MuriloLD/Projeto-AT-SP/Peças 3D/chave_On_Off/Bot/vistas_chaveOnOff_bot.PDF

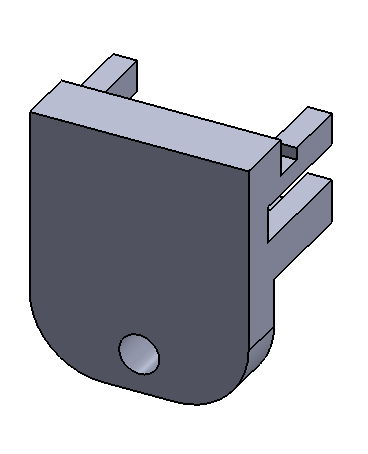
[picture p1: figure]
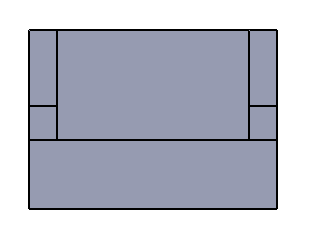
[picture p2: figure]
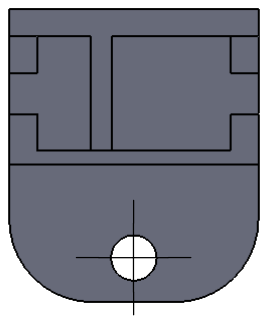
[picture p3: figure]
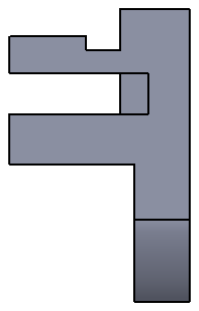
[picture p4: figure]
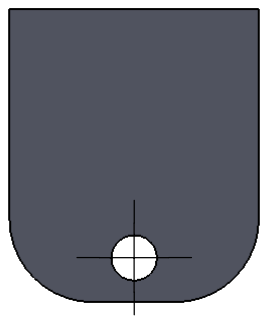
[picture p5: figure]
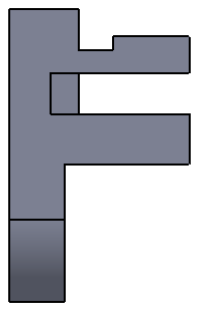
[picture p6: figure]
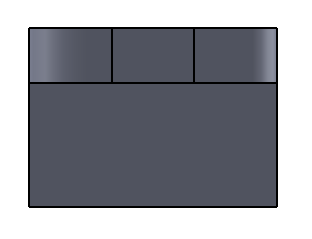
[picture p7: figure]
