MuriloLD/Projeto-AT-SP/Arquivos EAGLE/Shield ESP8266/shieldEsp_pcb.png

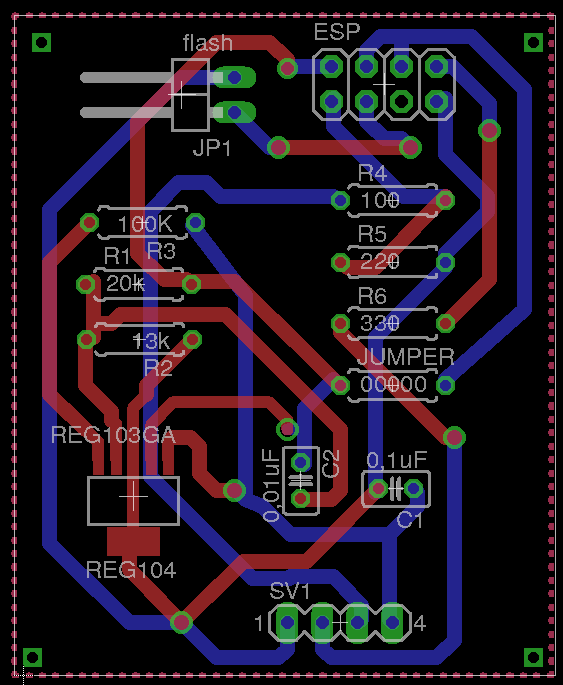
Arquivos EAGLE/Shield ESP8266/shieldEsp_pcb.png
