MuriloLD/Projeto-AT-SP/Peças 3D/case_bateria/Top/cotas.PNG

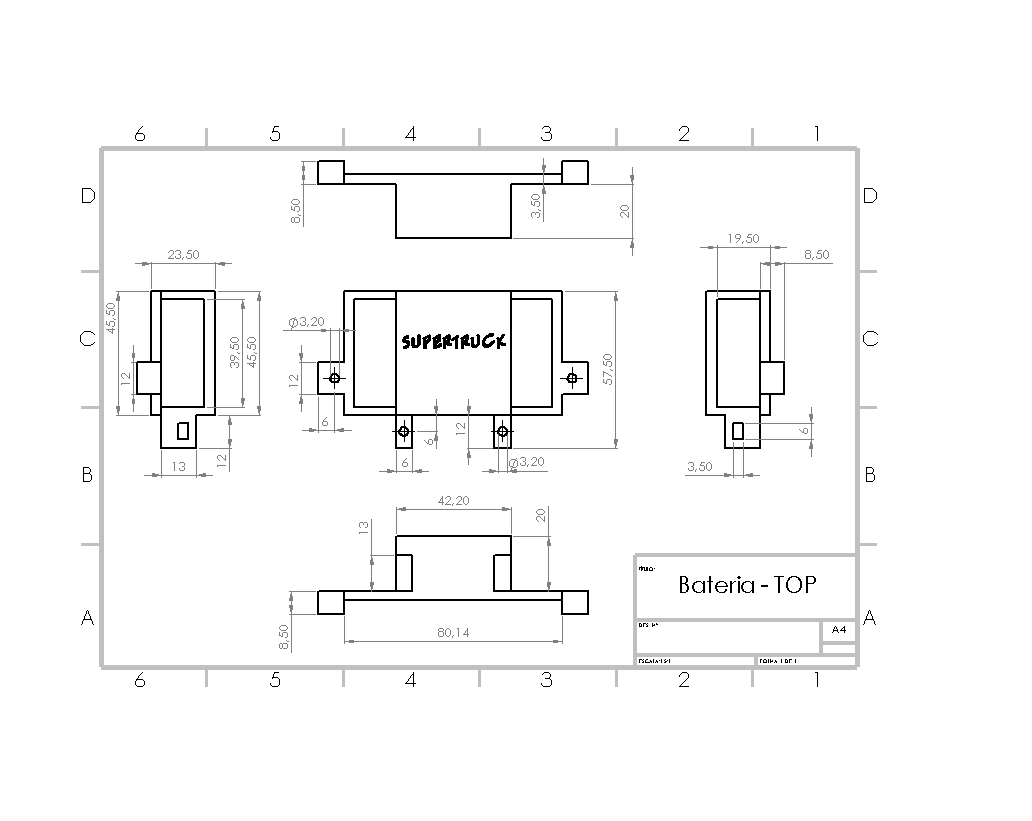
Peças 3D/case_bateria/Top/cotas.PNG
