MuriloLD/Projeto-AT-SP/Peças 3D/case_bateria/Top/vistas.PNG

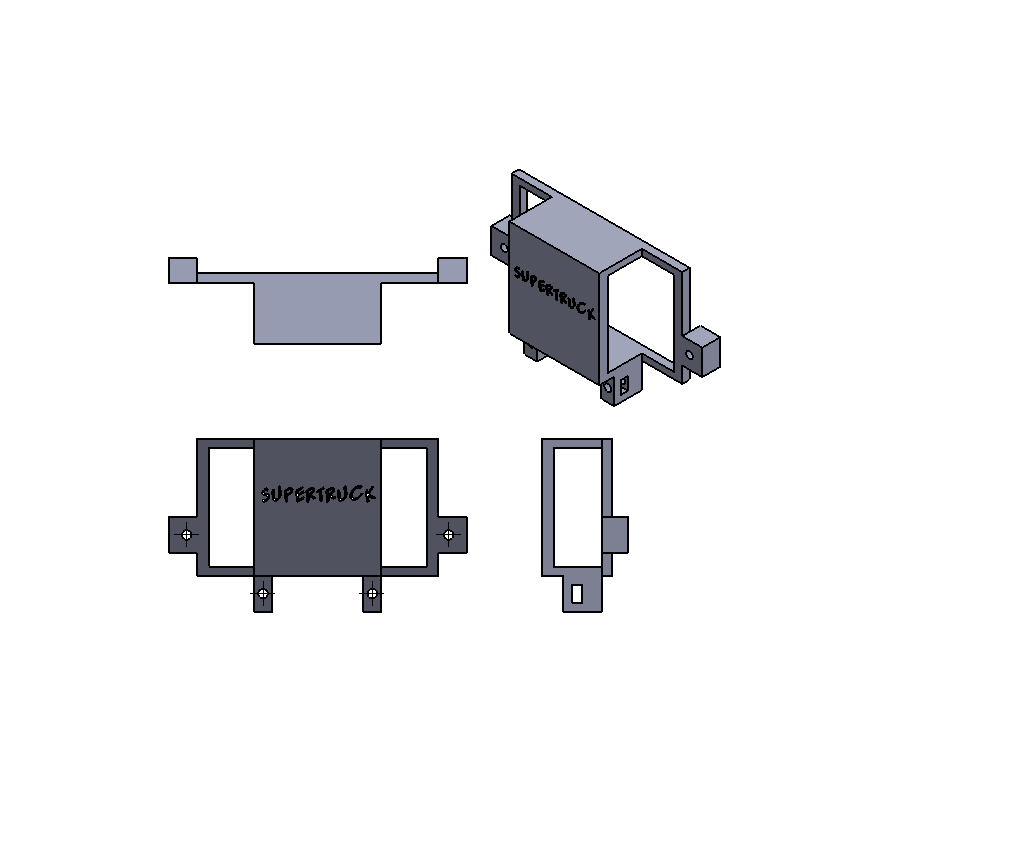
Peças 3D/case_bateria/Top/vistas.PNG
