MuriloLD/Projeto-AT-SP/Peças 3D/case_arduino_mega_stl/arduino_mega_top.stl

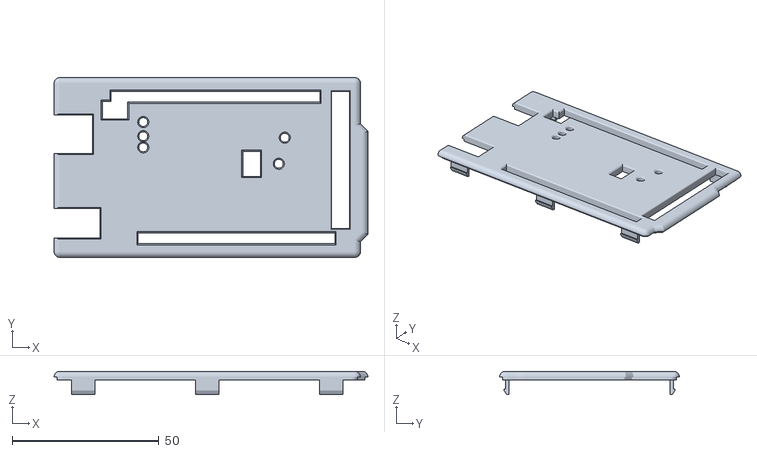
[picture p28: CAD file, 2016-11-09]
Peças 3D/case_arduino_mega_stl/arduino_mega_top.stl
107.1 x 61.3 x 8.00
