MuriloLD/Projeto-AT-SP/Peças 3D/suporte_arduino_mega_stl/Support carte AR Arduino.stl

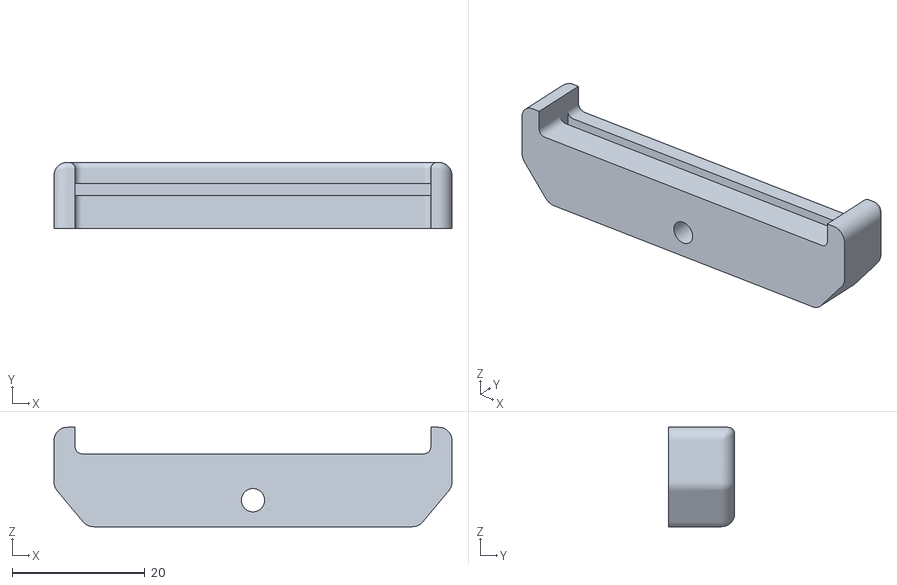
[picture p29: CAD file, 2016-11-09]
Peças 3D/suporte_arduino_mega_stl/Support carte AR Arduino.stl
60.0 x 10.0 x 15.0
