MuriloLD/Projeto-AT-SP/Peças 3D/suporte_ESP8266/Suporte_ESP8266_v4 - P3.SLDPRT

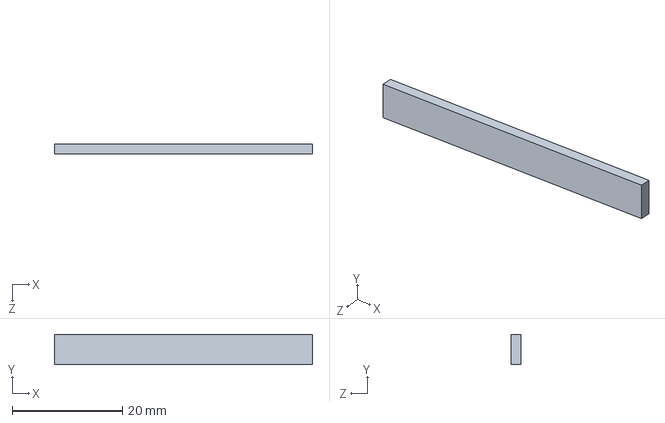
[picture p30: CAD file, 2016-11-09]
Peças 3D/suporte_ESP8266/Suporte_ESP8266_v4 - P3.SLDPRT
46.8 x 5.50 x 1.75 mm
