MuriloLD/Projeto-AT-SP/Peças 3D/suporte_ESP8266/Montagem1 - Suporte_ESP8266_v4 - P1-1.STL

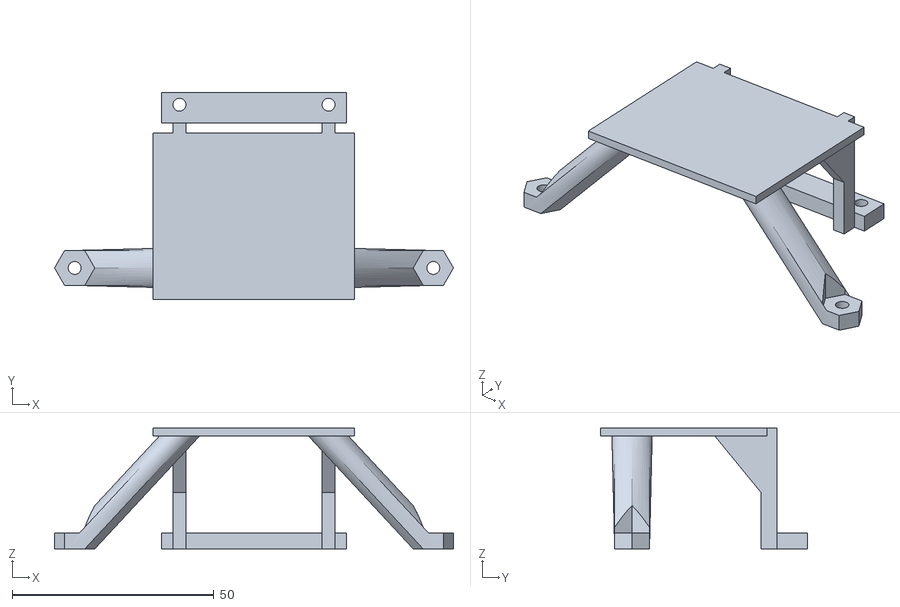
[picture p31: CAD file, 2016-11-09]
Peças 3D/suporte_ESP8266/Montagem1 - Suporte_ESP8266_v4 - P1-1.STL
99.0 x 51.3 x 30.0
