MuriloLD/Projeto-AT-SP/Peças 3D/suporte_ultrassom/US_Servo/cotas_ultrassom_servo.PDF

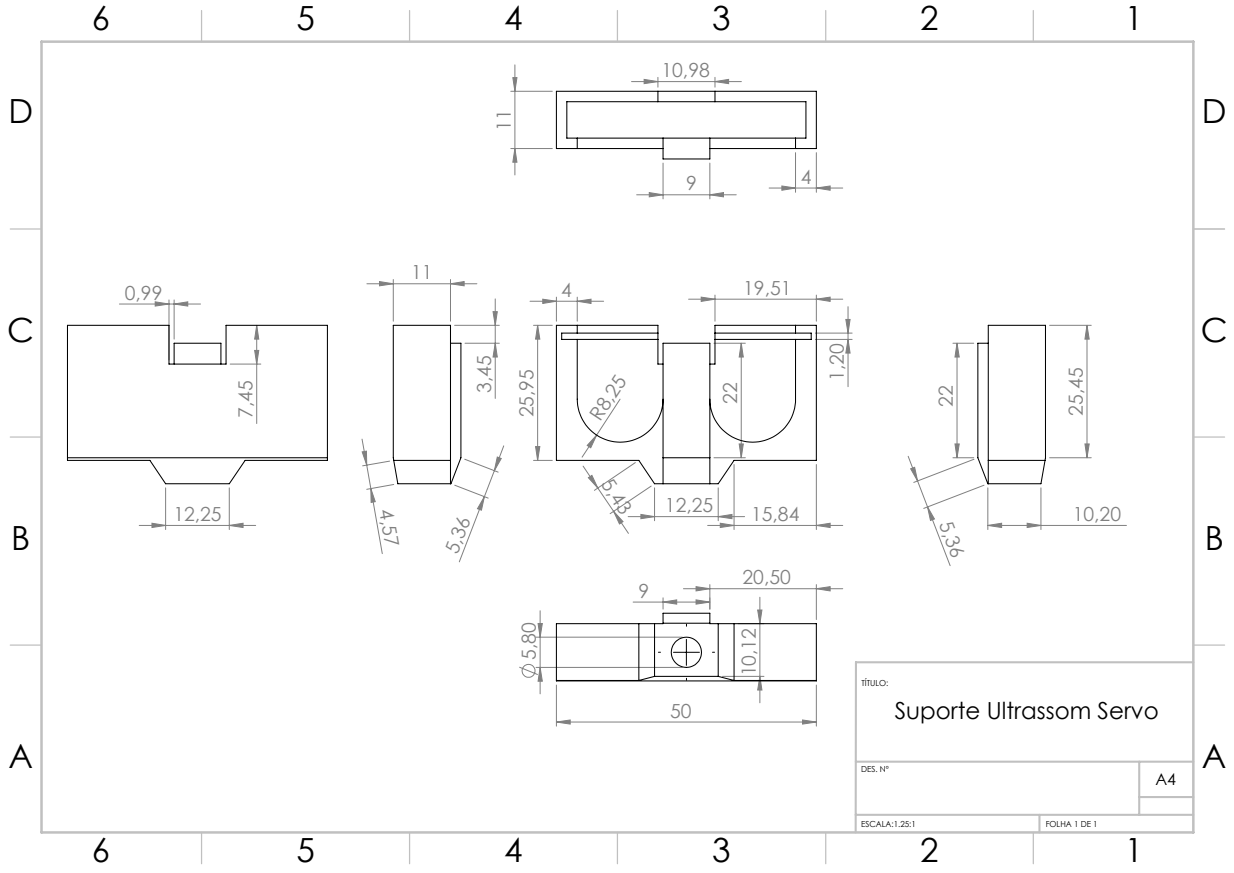
[picture p34: page 1]
DES. Nº; ESCALA:1.25:1; FOLHA 1 DE 1

TÍTULO:
Suporte Ultrassom Servo
