MuriloLD/Projeto-AT-SP/Arquivos EAGLE/Shield Arduino MEga/v4/Arduino_Circuito.pdf

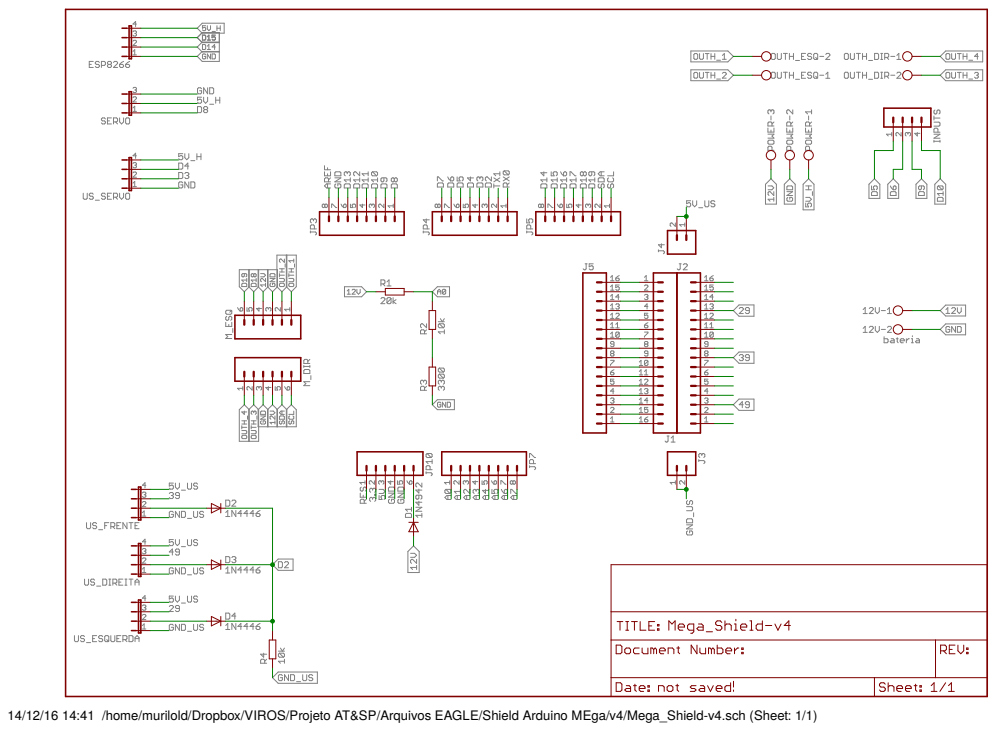
[picture p35: page 1]

14/12/16 14:41 /home/murilold/Dropbox/VIROS/Projeto AT&SP/Arquivos EAGLE/Shield Arduino MEga/v4/Mega_Shield-v4.sch (Sheet: 1/1)
