MuriloLD/Projeto-AT-SP/Arquivos EAGLE/Shield Arduino MEga/v4/Arduino_PCB.pdf

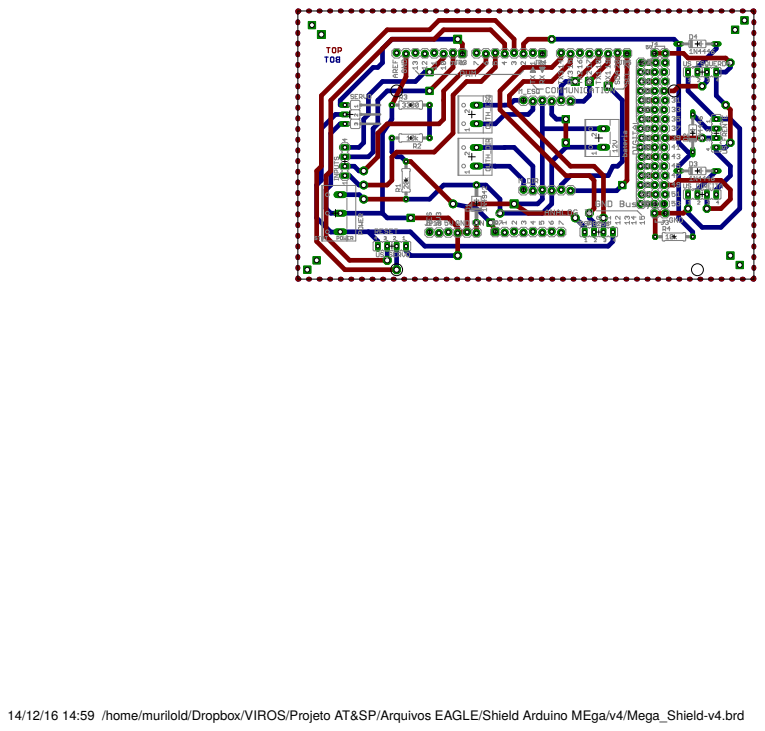
[picture p36: page 1]

14/12/16 14:59 /home/murilold/Dropbox/VIROS/Projeto AT&SP/Arquivos EAGLE/Shield Arduino MEga/v4/Mega_Shield-v4.brd
