MuriloLD/Projeto-AT-SP/Peças 3D/suporte_ultrassom/US_Servo/vistas_ultrassom_servo.PDF

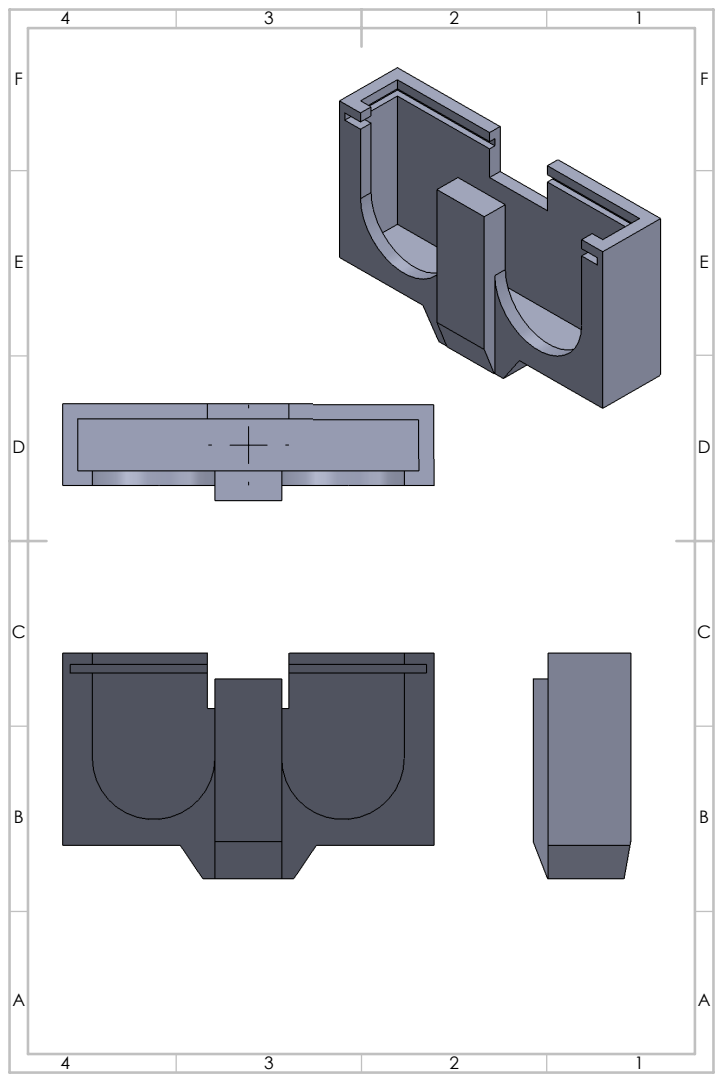
[picture p46: page 1]
