MuriloLD/Projeto-AT-SP/Peças 3D/suporte_ultrassom/US_simples/cotas_ultrassom_simpels.PDF

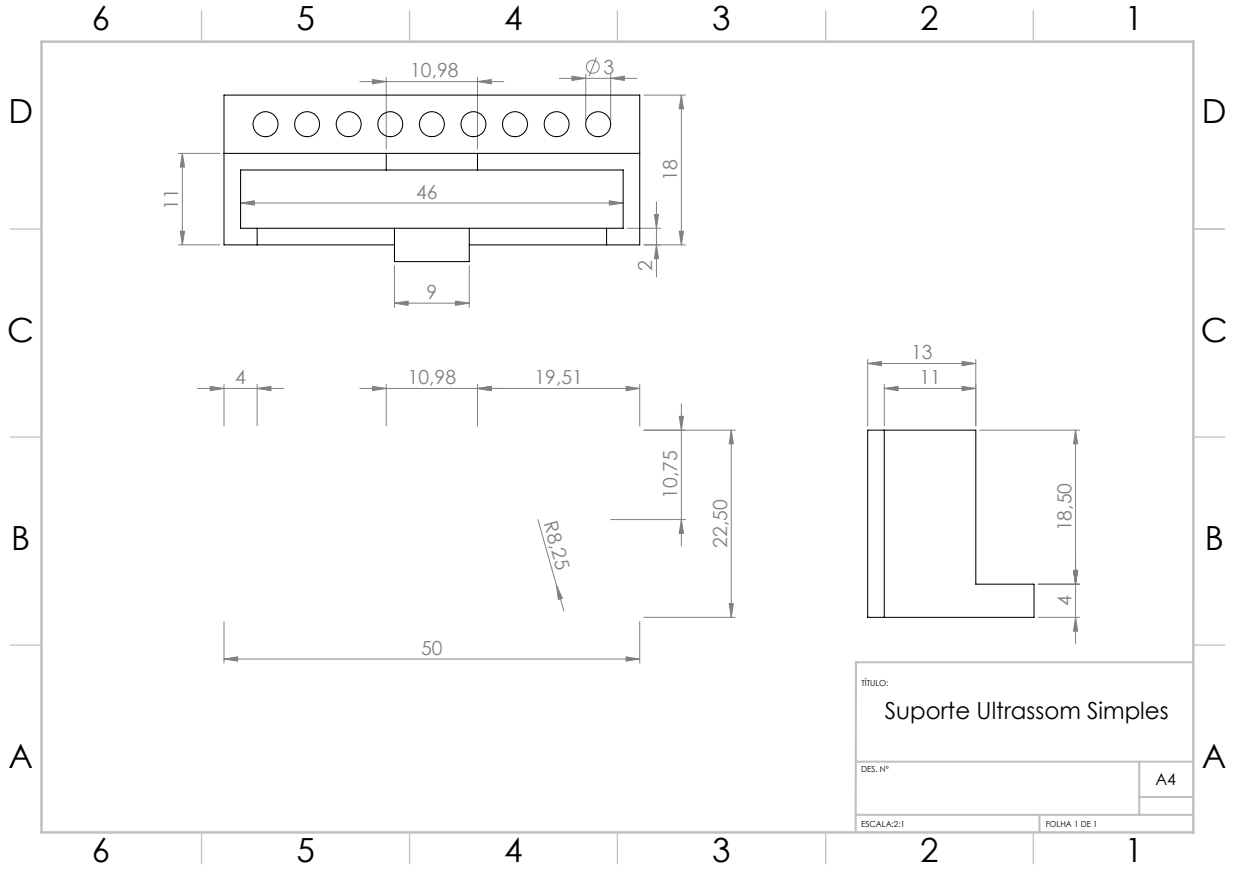
[picture p47: page 1]
DES. Nº; ESCALA:2:1; FOLHA 1 DE 1

TÍTULO:
Suporte Ultrassom Simples
