MuriloLD/Projeto-AT-SP/Peças 3D/suporte_ultrassom/US_simples/vistas_ultrassom_simpels.PDF

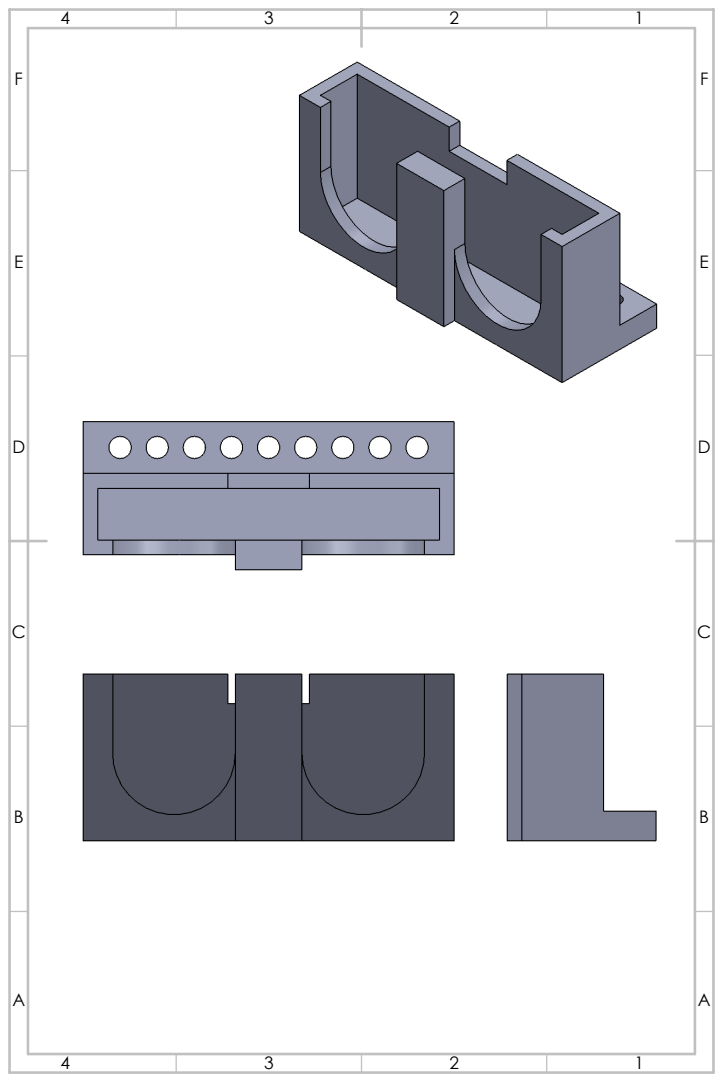
[picture p48: page 1]
