MuriloLD/Projeto-AT-SP/Peças 3D/case_bateria/Bot/cotas_SuporteBateria_BOT.PDF

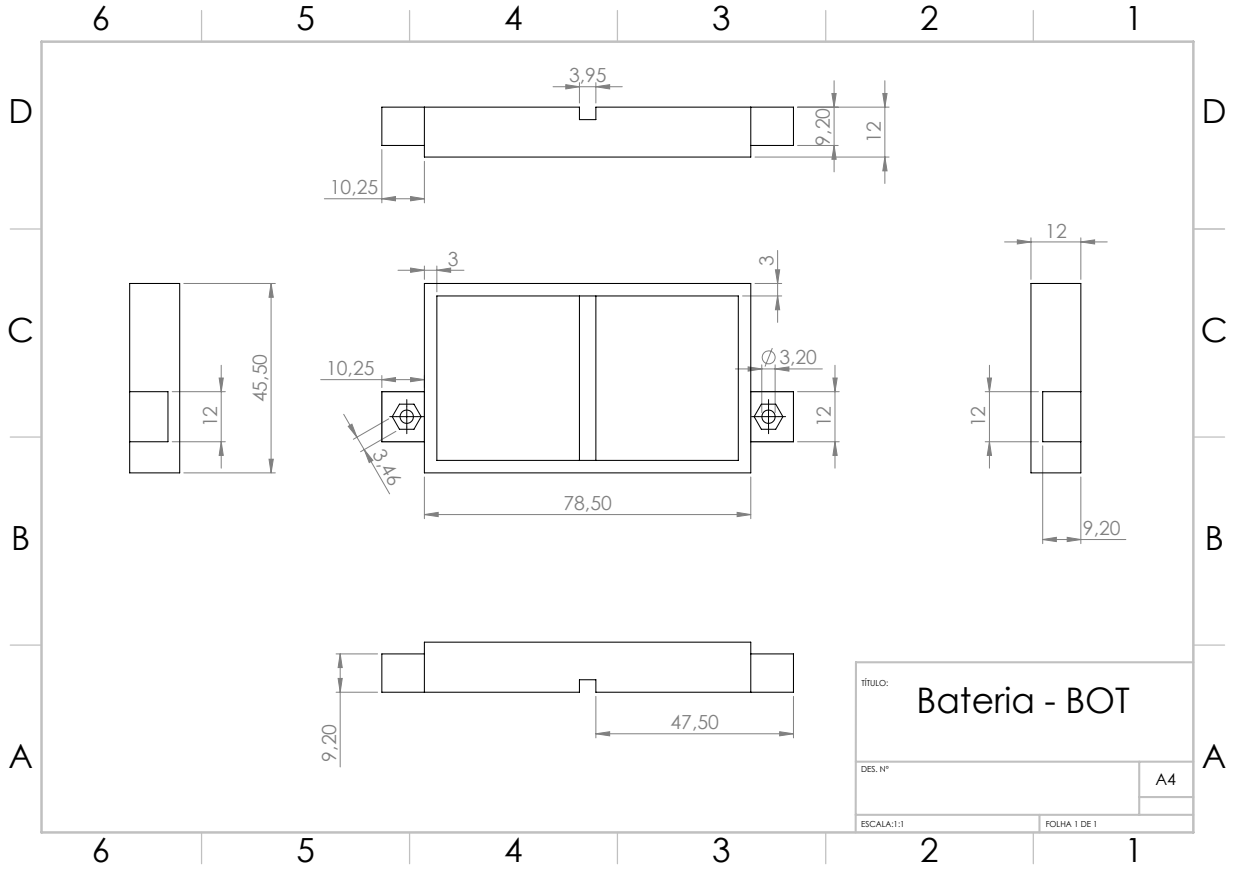
[picture p49: page 1]
DES. Nº; ESCALA:1:1; FOLHA 1 DE 1; Bateria - BOT
