MuriloLD/Projeto-AT-SP/Peças 3D/case_bateria/Bot/vistas_SuporteBateria_BOT.PDF

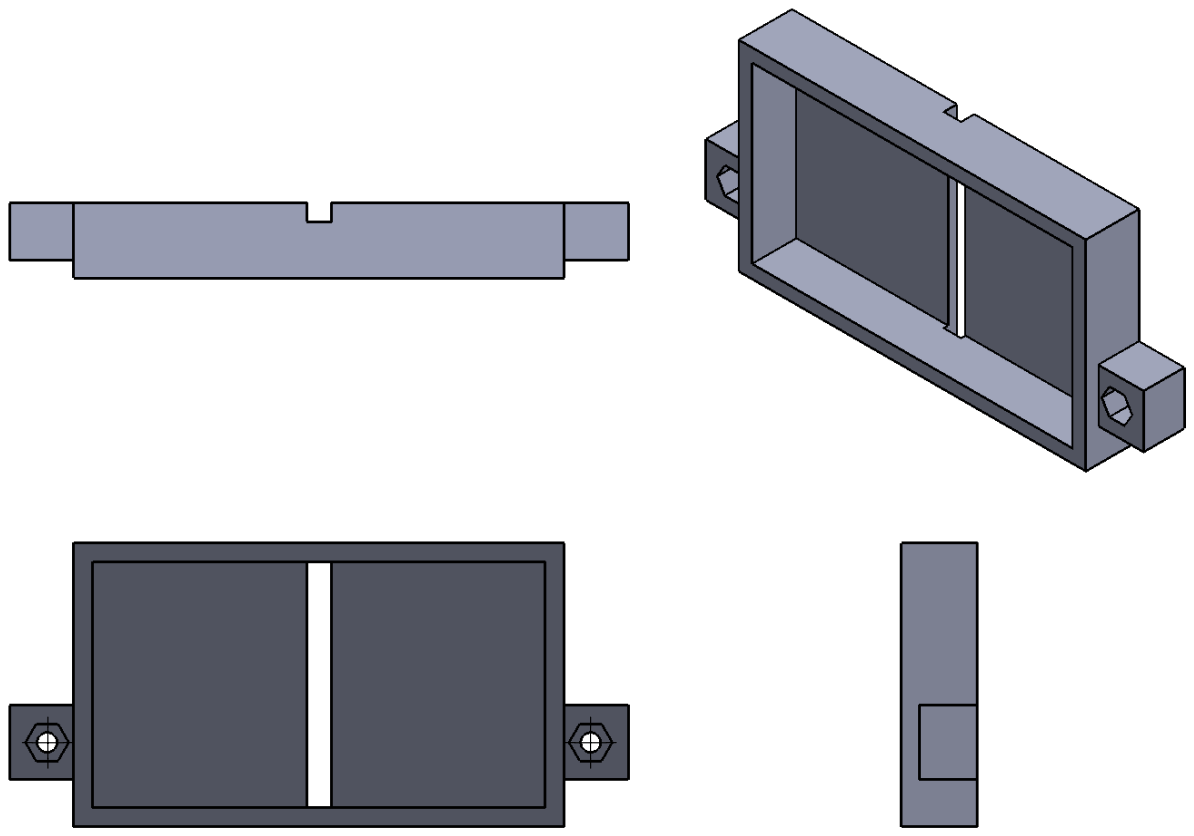
[picture p50: page 1]
