MuriloLD/Projeto-AT-SP/Peças 3D/case_bateria/Top/cotas_SuporteBateria_TOP.PDF

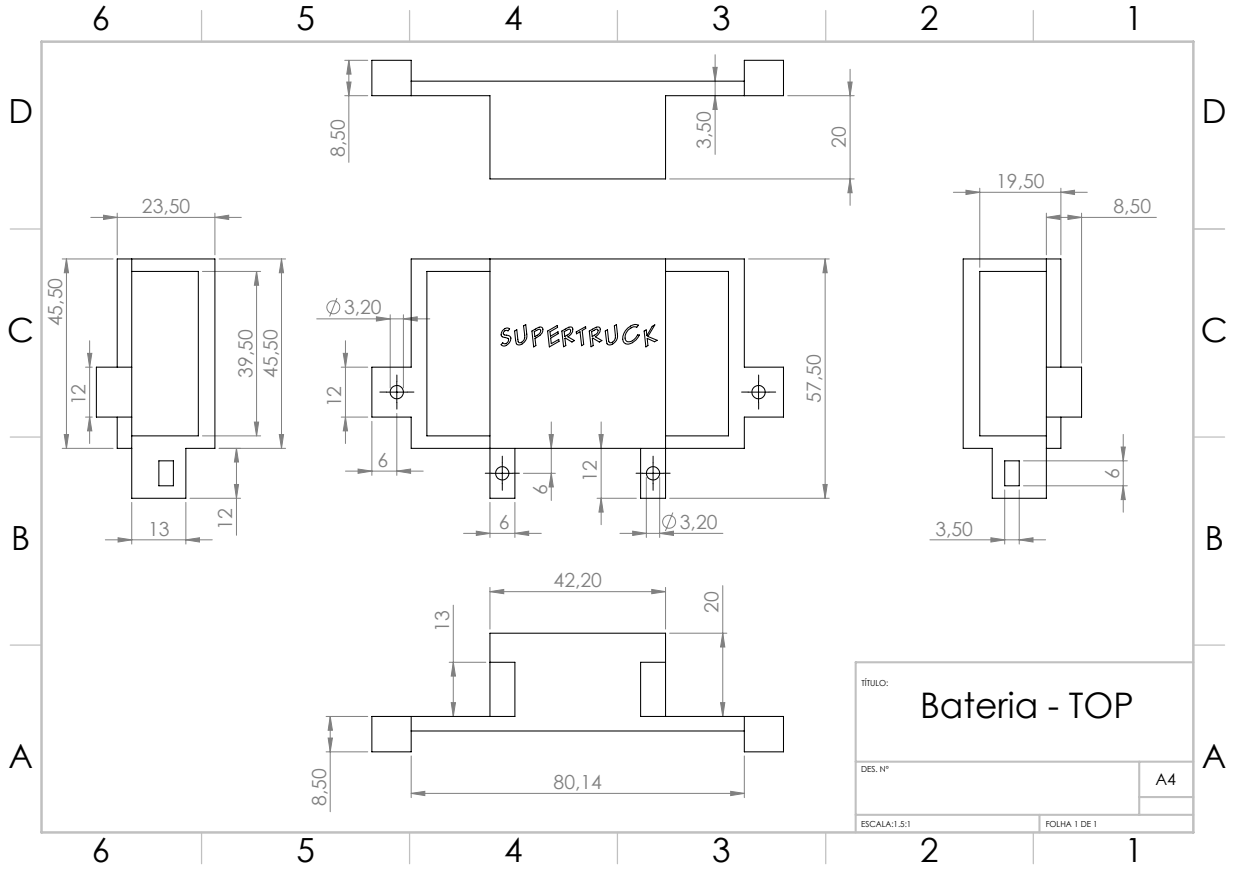
[picture p51: page 1]
DES. Nº; ESCALA:1.5:1; FOLHA 1 DE 1; Bateria - TOP
