MuriloLD/Projeto-AT-SP/Peças 3D/case_bateria/Top/vistas_SuporteBateria_TOP.PDF

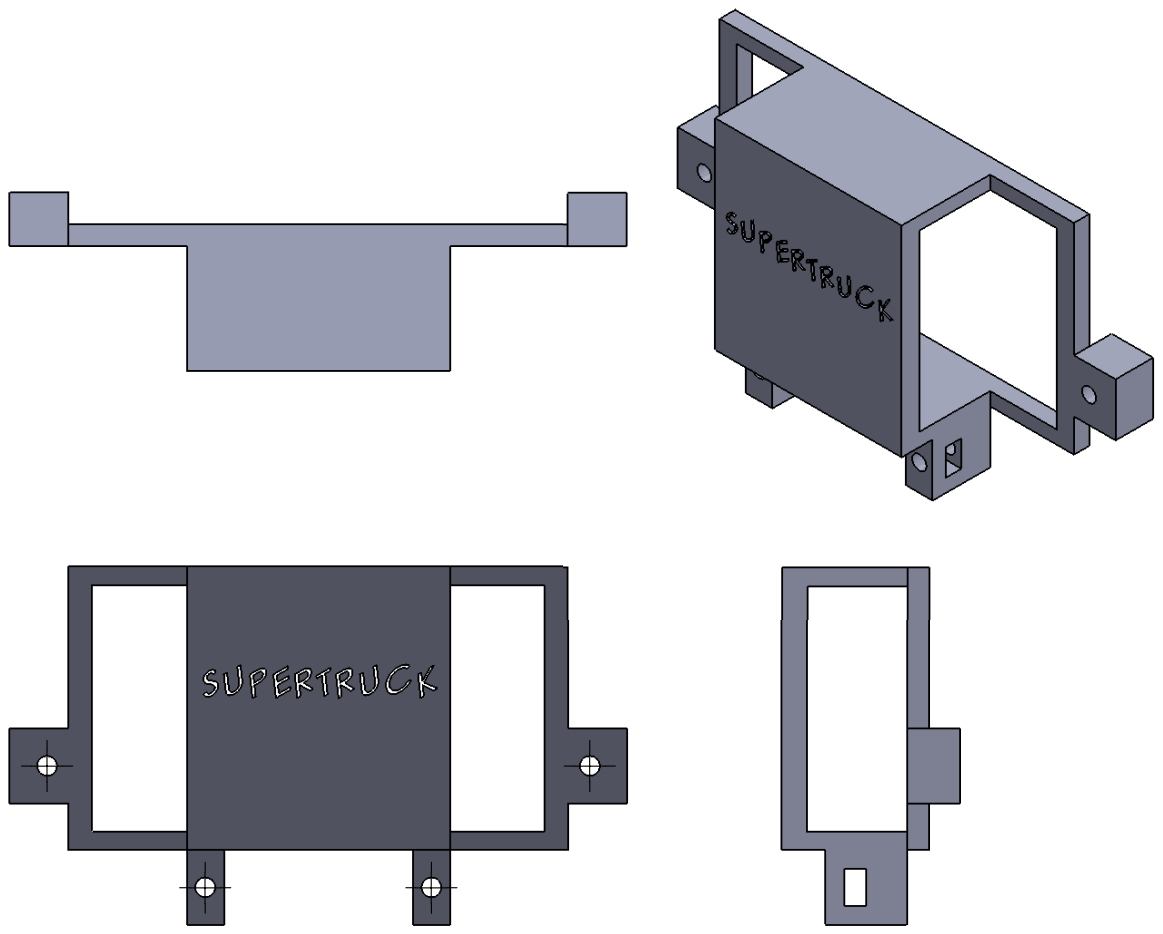
[picture p52: page 1]
