MuriloLD/Projeto-AT-SP/Peças 3D/chave_On_Off/Bot/cotas_chaveOnOff_bot.PDF

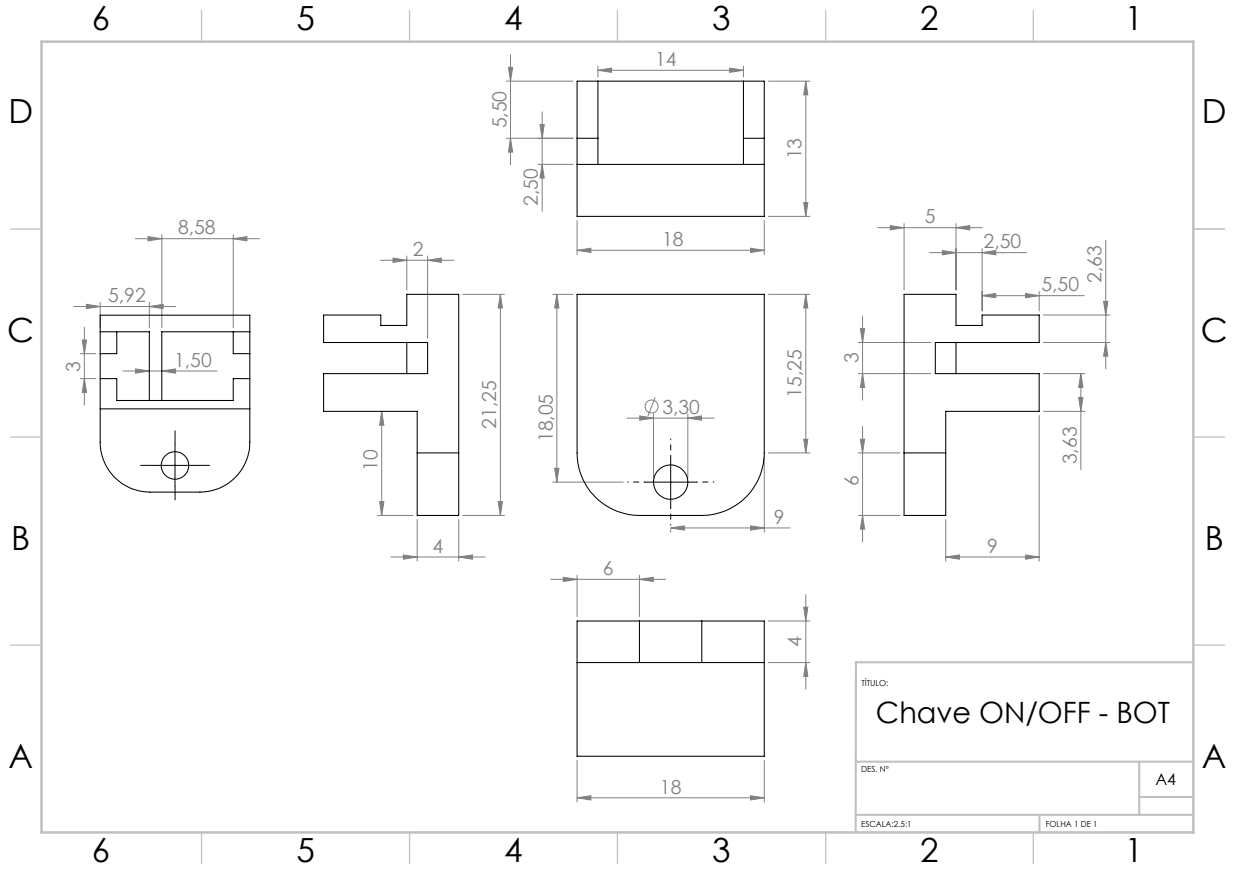
[picture p53: page 1]
DES. Nº; ESCALA:2.5:1; FOLHA 1 DE 1

Chave ON/OFF - BOT
