MuriloLD/Projeto-AT-SP/Peças 3D/chave_On_Off/Top/cotas_chaveOnOff_top.PDF

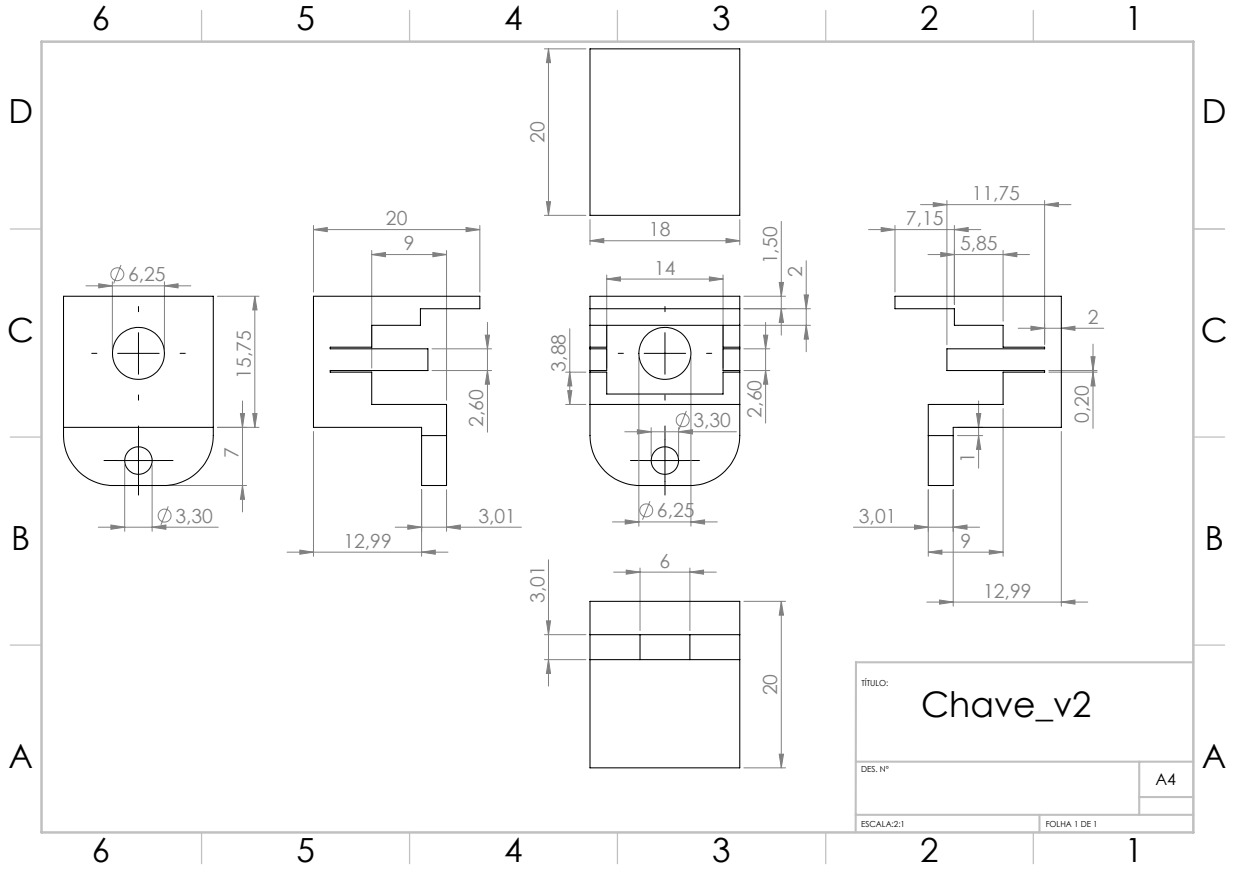
[picture p54: page 1]
DES. Nº; ESCALA:2:1; FOLHA 1 DE 1
