MuriloLD/Projeto-AT-SP/Peças 3D/chave_On_Off/Top/vistas_chaveOnOff_top.PDF

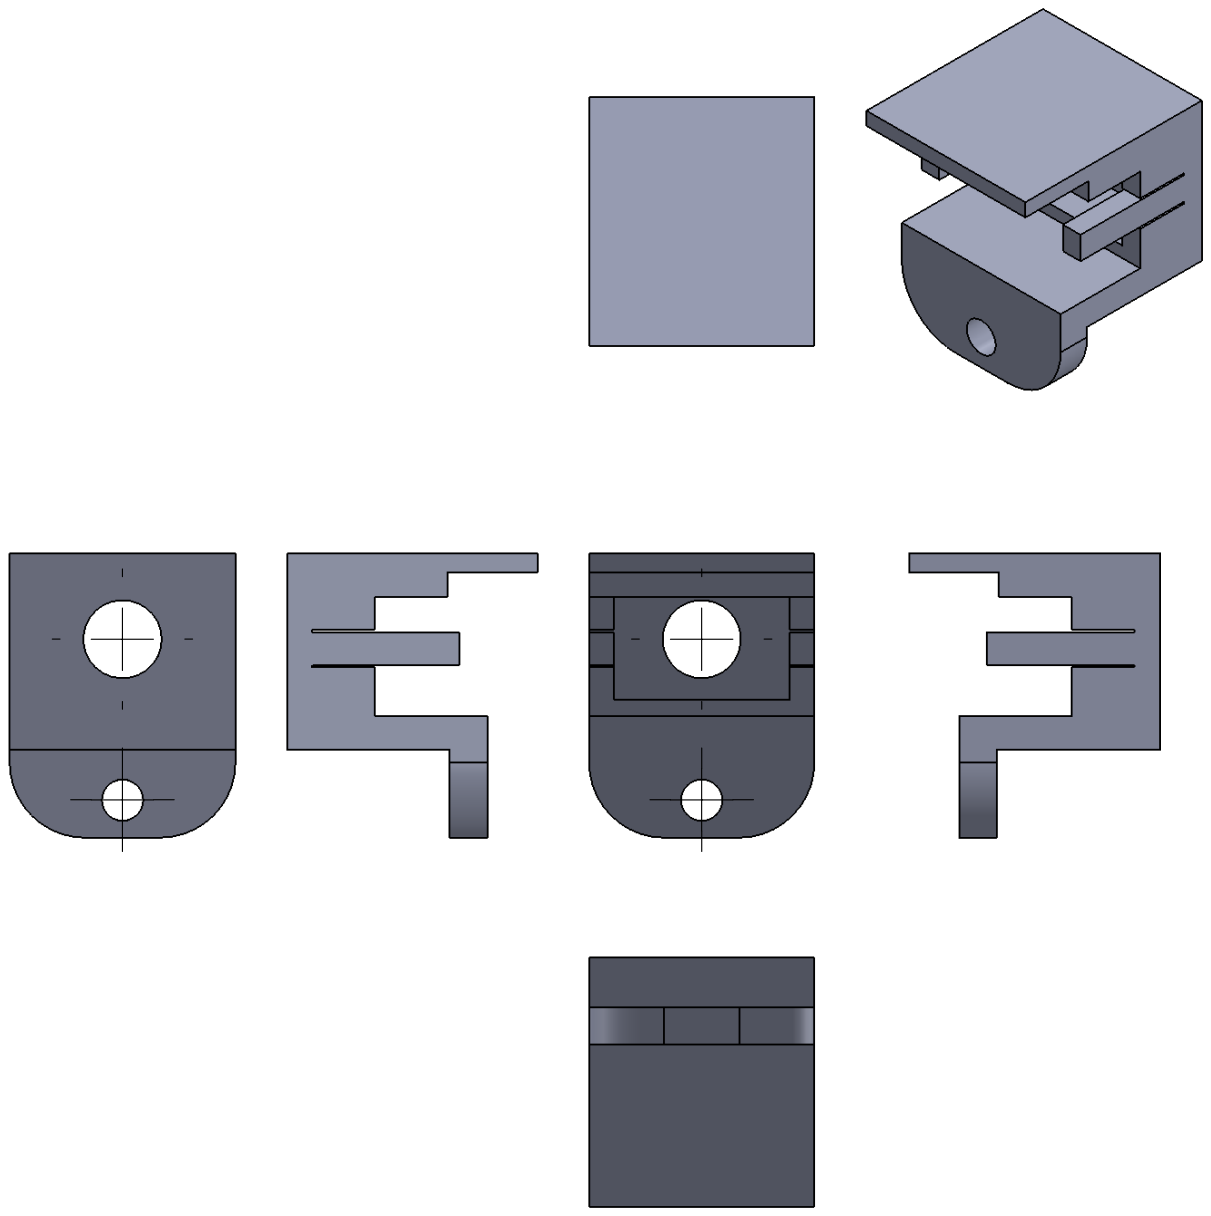
[picture p55: page 1]
