MuriloLD/Projeto-AT-SP/Arquivos EAGLE/Shield Arduino MEga/v4/1BOT.pdf

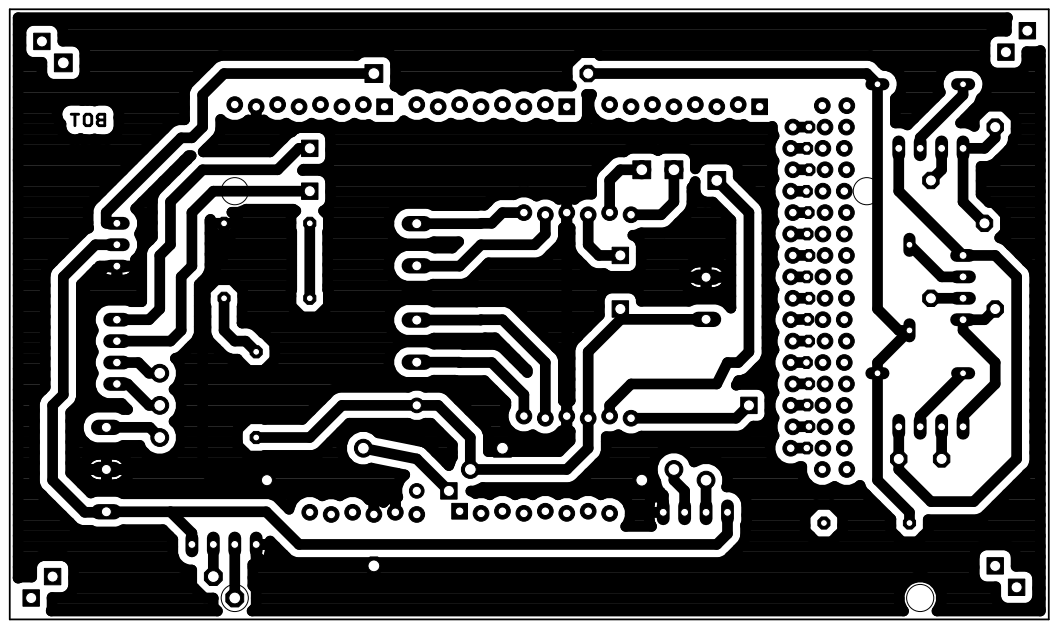
[picture p56: page 1]
