MuriloLD/Projeto-AT-SP/Arquivos EAGLE/Shield Arduino MEga/v4/1TOP.pdf

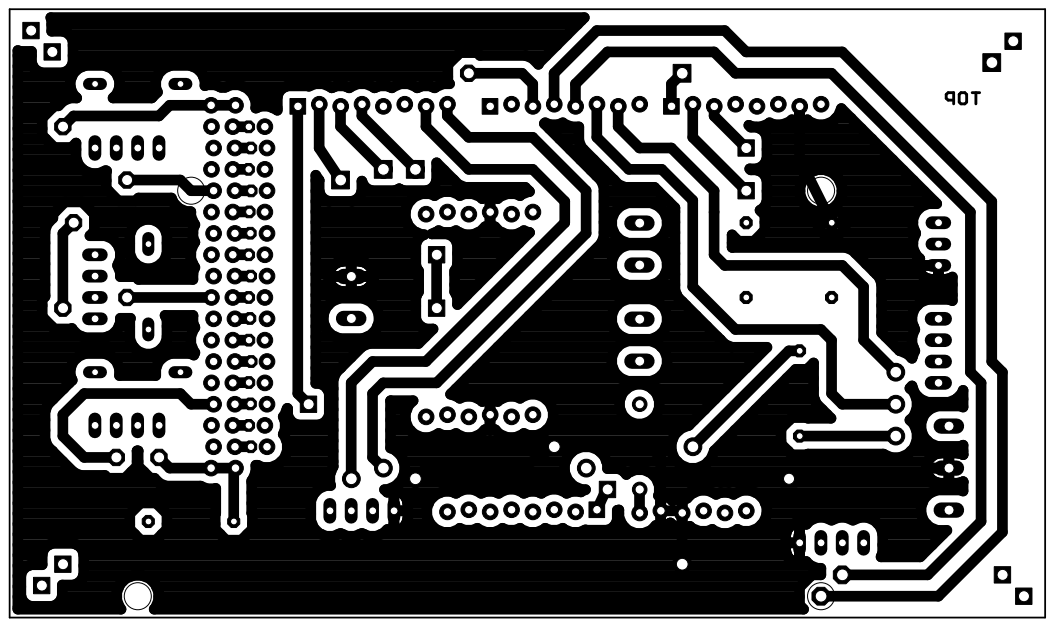
[picture p57: page 1]
