MuriloLD/Projeto-AT-SP/Arquivos EAGLE/Shield Arduino MEga/v4/2BOT.pdf

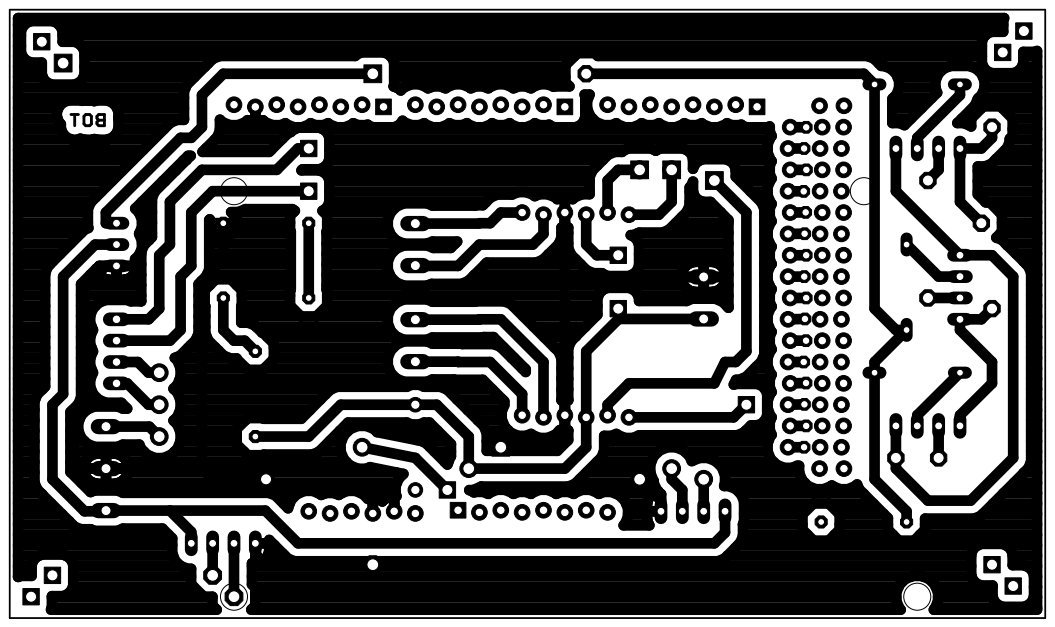
[picture p58: page 1]
