MuriloLD/Projeto-AT-SP/Arquivos EAGLE/Shield Arduino MEga/v4/2TOP.pdf

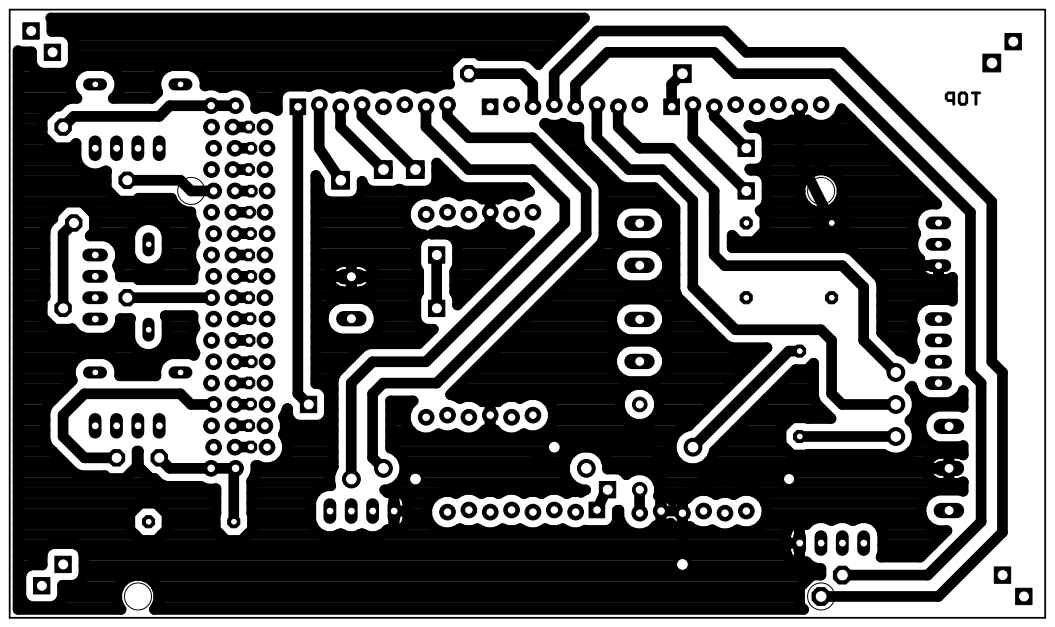
[picture p59: page 1]
